andreabenini/beholder/hardware/rollie-Base.stl

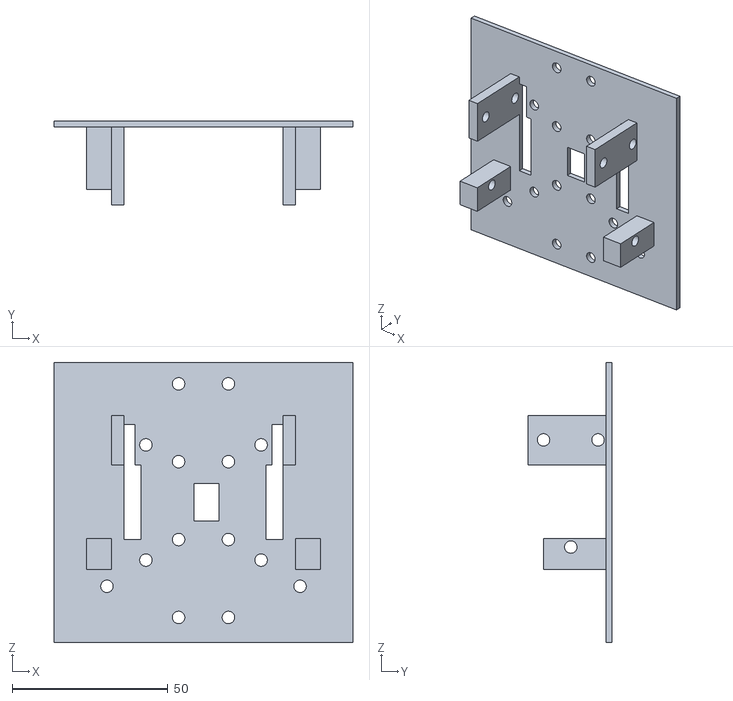
[picture p17: CAD file, 2023-04-09]
hardware/rollie-Base.stl
96.0 x 27.0 x 90.0
