andreabenini/beholder/hardware/rollie.3.0/rollie3-Right Bearing InnerConnector.stl

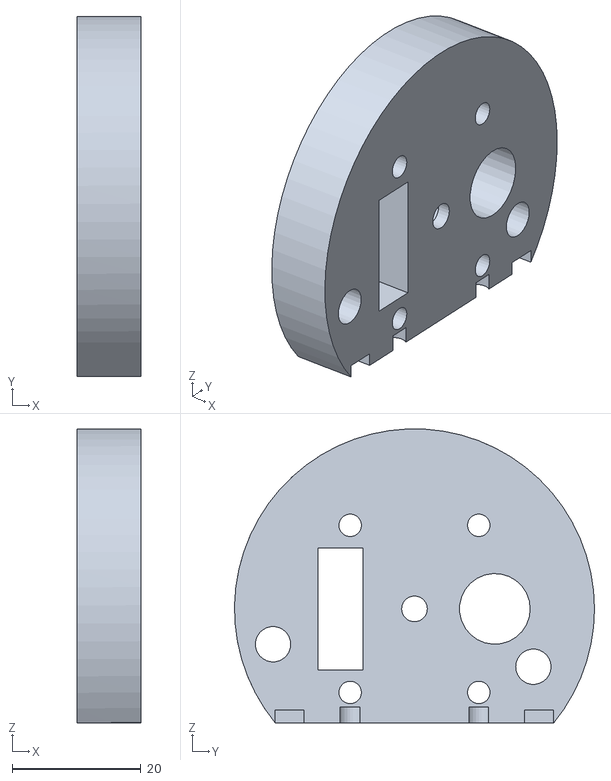
[picture p18: CAD file, 2023-11-20]
hardware/rollie.3.0/rollie3-Right Bearing InnerConnector.stl
10.0 x 56.0 x 45.7
