andreabenini/beholder/hardware/2.0/rollie2-wheel Right Inner Back.stl

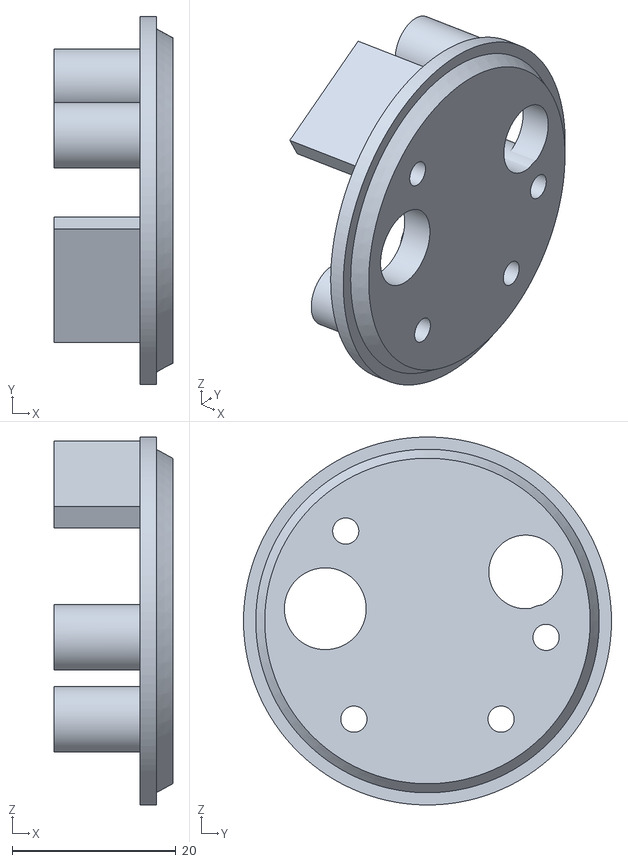
[picture p19: CAD file, 2023-09-27]
hardware/2.0/rollie2-wheel Right Inner Back.stl
14.5 x 45.0 x 45.0
