andreabenini/beholder/hardware/microguard.1.0/microguard-cylinder spacer1.stl

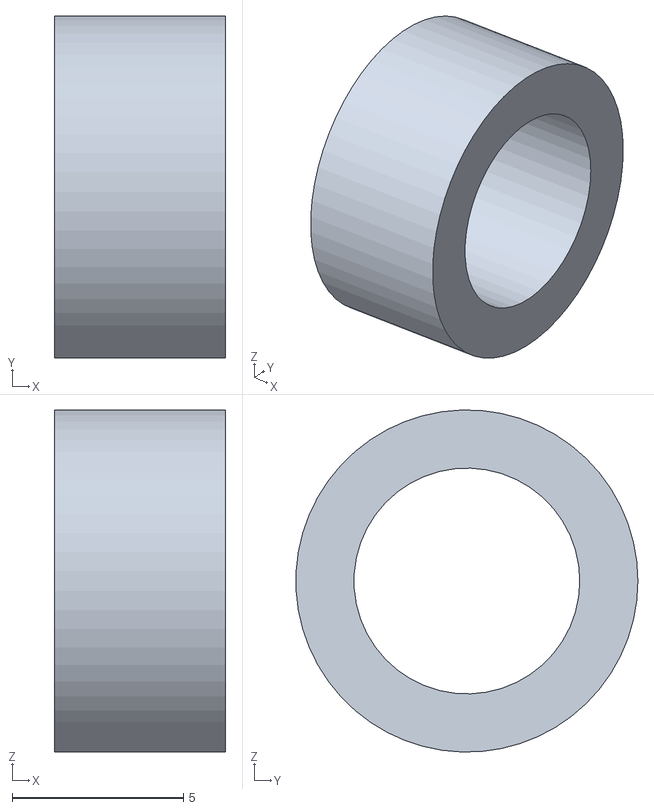
[picture p20: CAD file, 2024-03-03]
hardware/microguard.1.0/microguard-cylinder spacer1.stl
5.00 x 9.99 x 10.00
