andreabenini/beholder/hardware/rollie.3.0/rollie3-Right Bearing Inner Back.stl

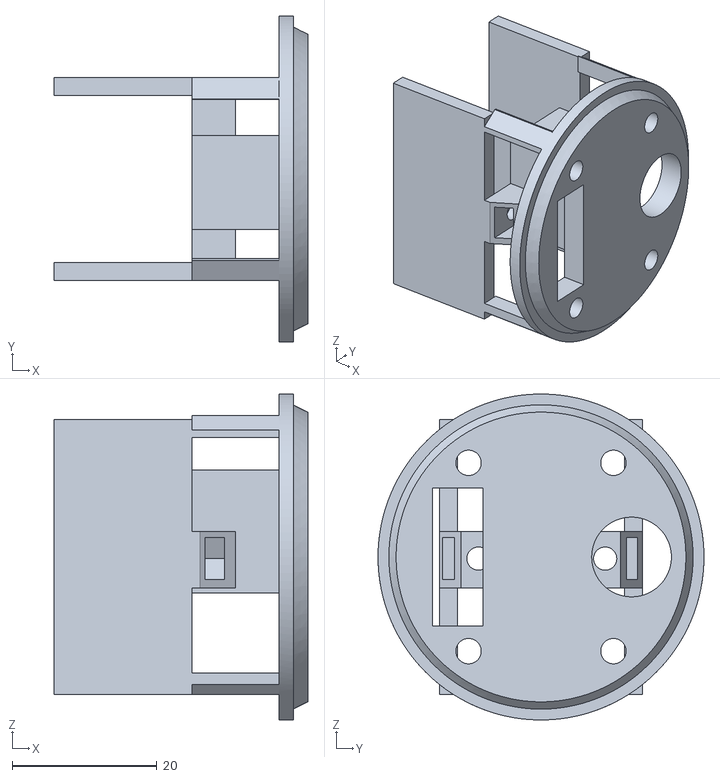
[picture p21: CAD file, 2023-11-20]
hardware/rollie.3.0/rollie3-Right Bearing Inner Back.stl
35.0 x 45.0 x 45.0
