andreabenini/beholder/hardware/2.0/rollie2-wheel Left Inner Back.stl

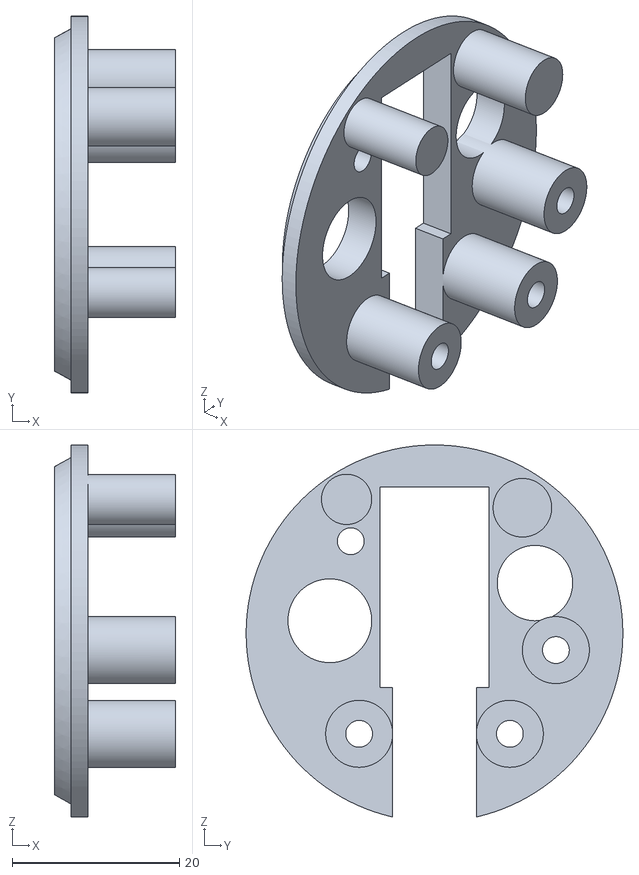
[picture p22: CAD file, 2023-09-27]
hardware/2.0/rollie2-wheel Left Inner Back.stl
14.5 x 45.0 x 44.4
