andreabenini/beholder/hardware/microguard.1.0/microguard-caster wheel holder.stl

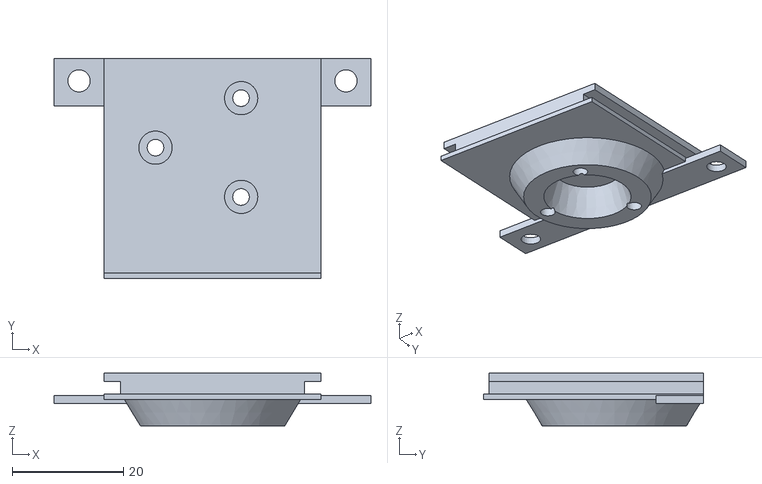
[picture p23: CAD file, 2024-03-01]
hardware/microguard.1.0/microguard-caster wheel holder.stl
57.0 x 39.5 x 9.50
