andreabenini/beholder/hardware/2.0/rollie2-Battery Holder Right.stl

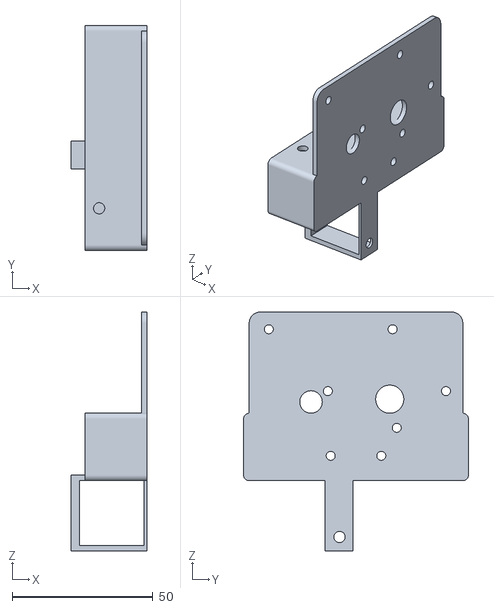
[picture p24: CAD file, 2023-09-22]
hardware/2.0/rollie2-Battery Holder Right.stl
27.0 x 80.0 x 85.0
