andreabenini/beholder/hardware/microguard.1.0/microguard-Controller Deck.stl

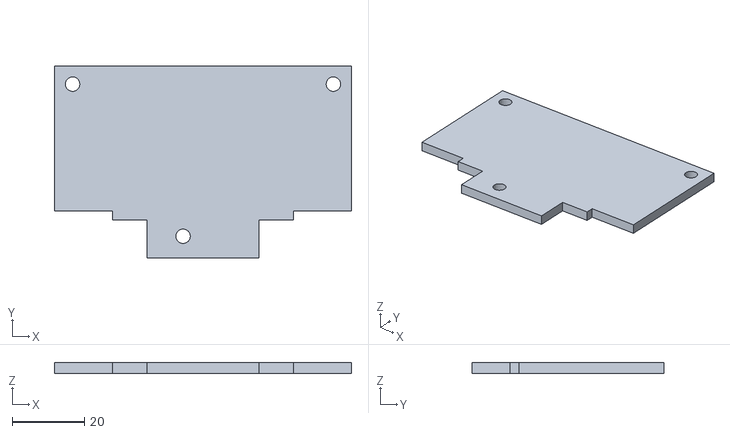
[picture p25: CAD file, 2024-03-01]
hardware/microguard.1.0/microguard-Controller Deck.stl
82.0 x 53.0 x 3.00
