andreabenini/beholder/hardware/rollie.3.0/rollie3-Left Pinion Gear.stl

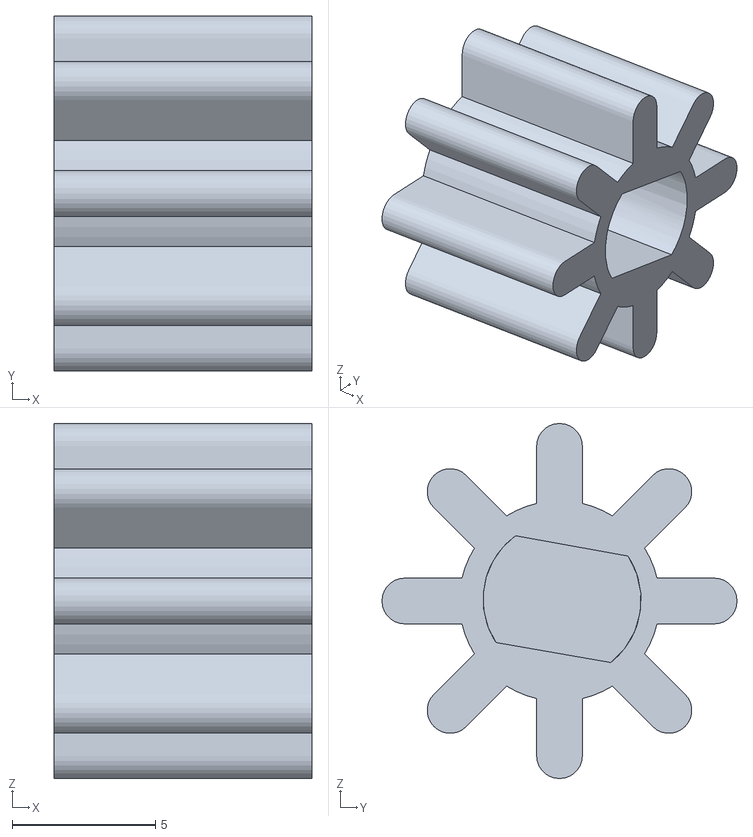
[picture p26: CAD file, 2023-11-13]
hardware/rollie.3.0/rollie3-Left Pinion Gear.stl
9.00 x 12.4 x 12.4
