andreabenini/beholder/hardware/2.0/rollie2-wheel Right Gear Pinion.stl

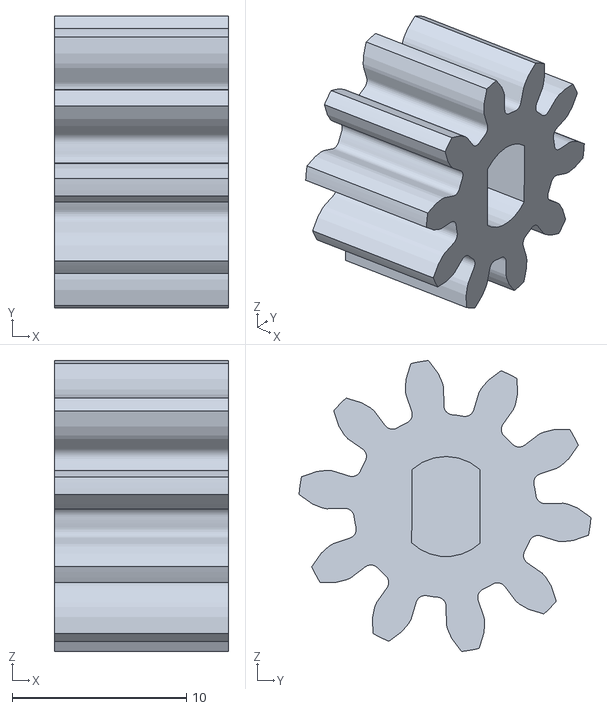
[picture p27: CAD file, 2023-07-04]
hardware/2.0/rollie2-wheel Right Gear Pinion.stl
10.0 x 16.7 x 16.7
