andreabenini/beholder/hardware/microguard.1.0/microguard-motor holder.stl

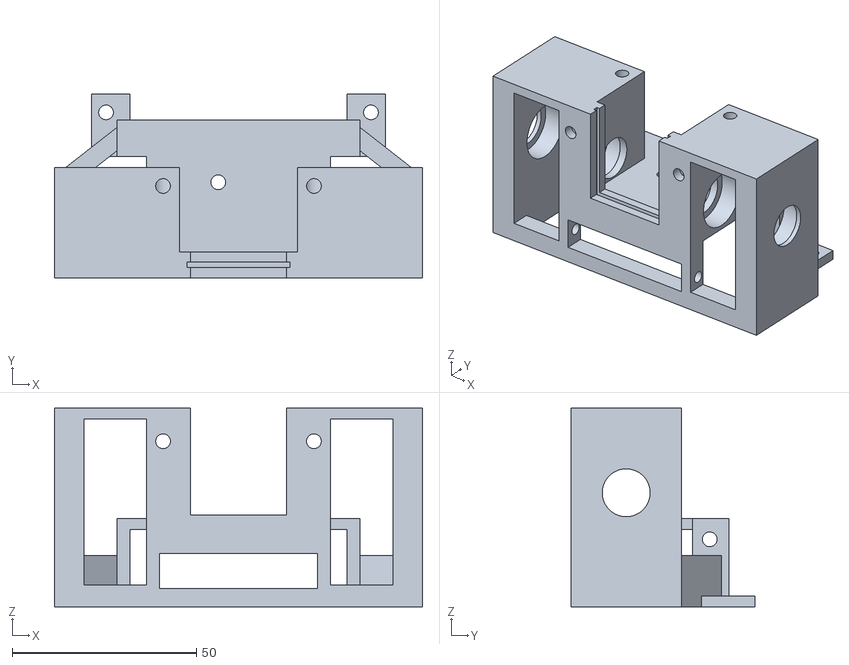
[picture p28: CAD file, 2024-02-28]
hardware/microguard.1.0/microguard-motor holder.stl
100.0 x 50.0 x 54.0
