andreabenini/beholder/hardware/rollie.3.0/rollie3-Left Bearing Inner Front.stl

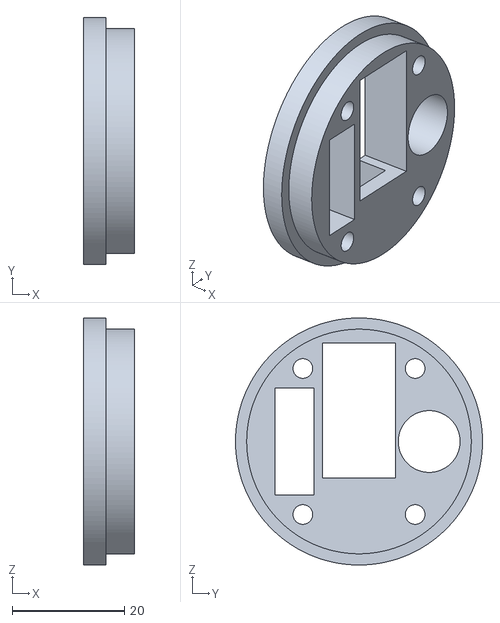
[picture p29: CAD file, 2023-11-12]
hardware/rollie.3.0/rollie3-Left Bearing Inner Front.stl
9.00 x 44.0 x 44.0
