andreabenini/beholder/hardware/2.0/rollie2-wheel Right Cap Front.stl

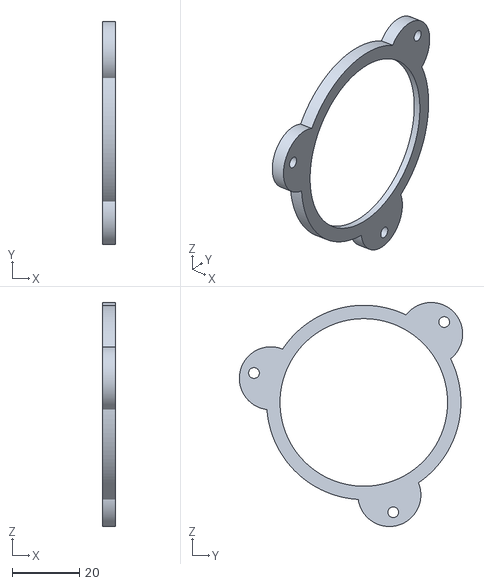
[picture p30: CAD file, 2023-06-18]
hardware/2.0/rollie2-wheel Right Cap Front.stl
4.00 x 66.7 x 66.9
