andreabenini/beholder/hardware/microguard.1.0/microguard-base plate.stl

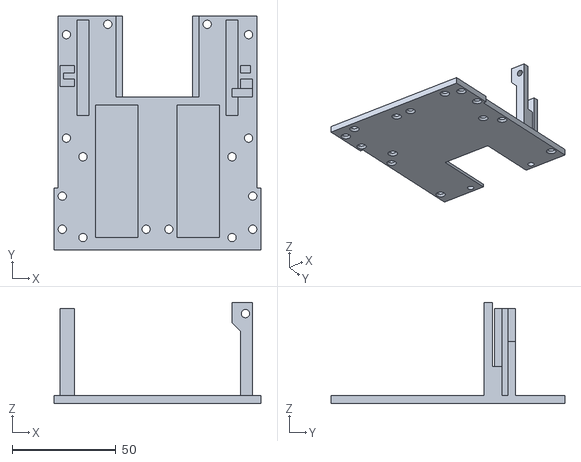
[picture p31: CAD file, 2024-02-24]
hardware/microguard.1.0/microguard-base plate.stl
100.0 x 113.0 x 49.0
