andreabenini/beholder/hardware/2.0/rollie2-Shoulder Right.stl

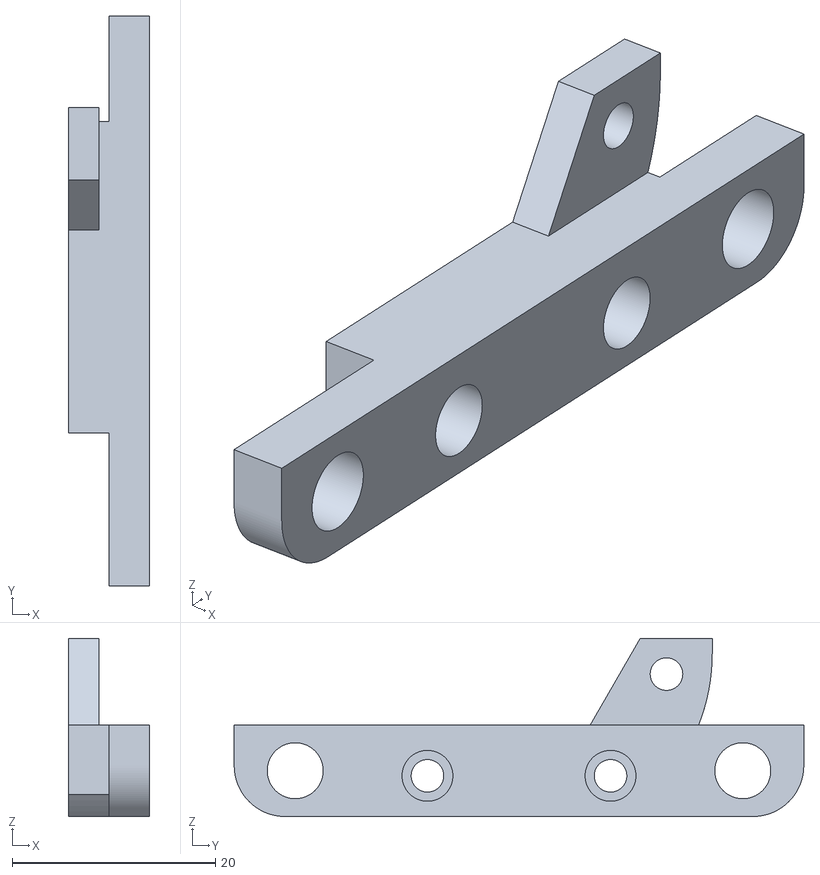
[picture p32: CAD file, 2023-06-18]
hardware/2.0/rollie2-Shoulder Right.stl
8.00 x 56.0 x 17.5
