andreabenini/beholder/hardware/microguard.1.0/microguard-mold side1.stl

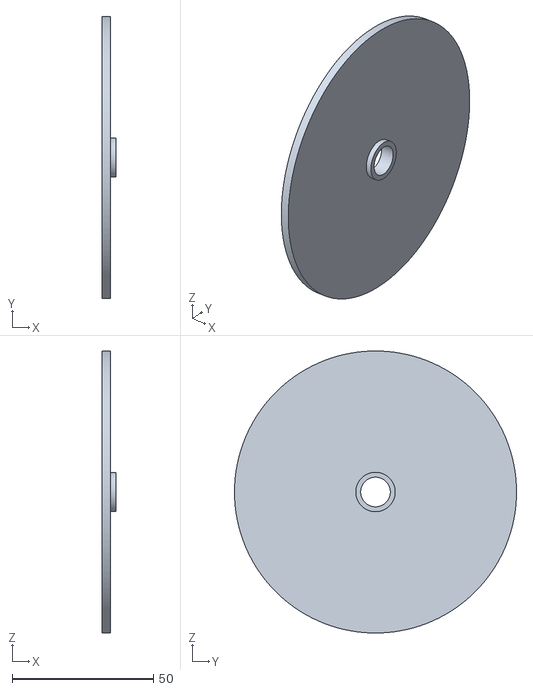
[picture p33: CAD file, 2024-01-27]
hardware/microguard.1.0/microguard-mold side1.stl
5.00 x 100.0 x 100.0
