andreabenini/beholder/hardware/rollie.3.0/rollie3-Left Bearing InnerConnector.stl

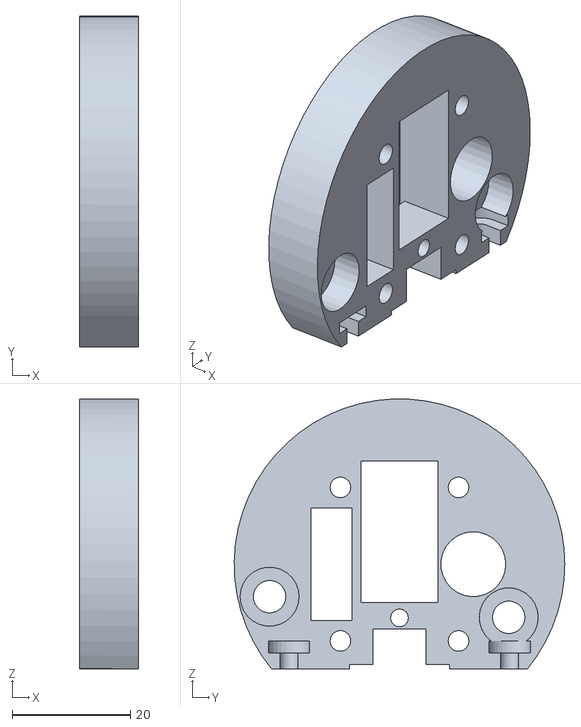
[picture p34: CAD file, 2023-11-11]
hardware/rollie.3.0/rollie3-Left Bearing InnerConnector.stl
10.0 x 56.0 x 45.7
