andreabenini/beholder/hardware/2.0/rollie2-servo Arm.stl

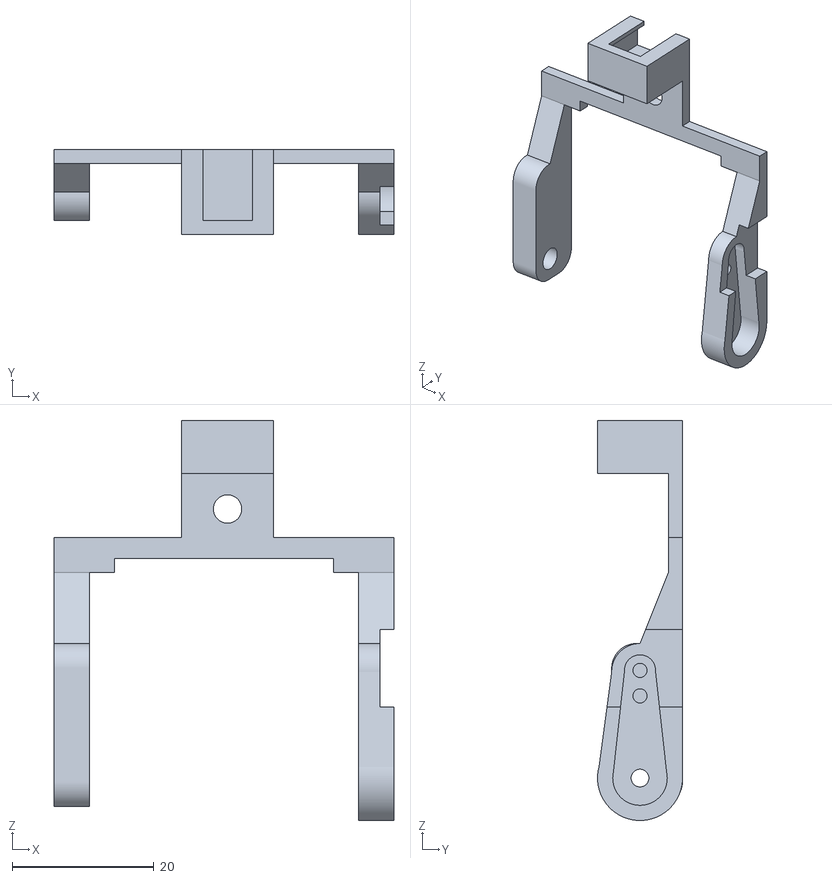
[picture p35: CAD file, 2023-06-15]
hardware/2.0/rollie2-servo Arm.stl
48.0 x 12.0 x 56.5
