andreabenini/beholder/hardware/microguard.1.0/microguard-mold side2.stl

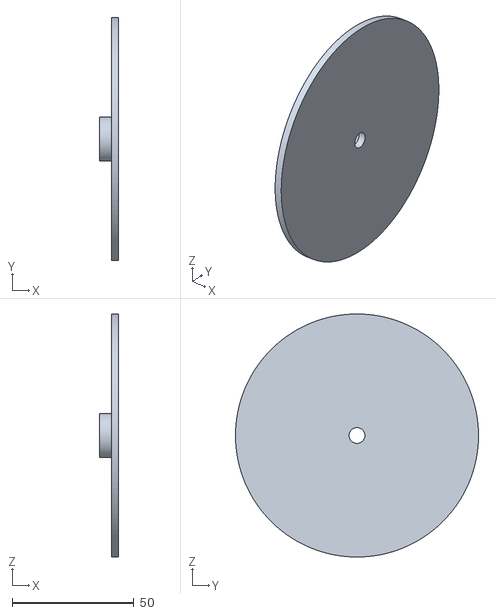
[picture p36: CAD file, 2024-01-27]
hardware/microguard.1.0/microguard-mold side2.stl
8.00 x 100.0 x 100.0
