andreabenini/beholder/hardware/rollie.3.0/rollie3-Holder Spacer.stl

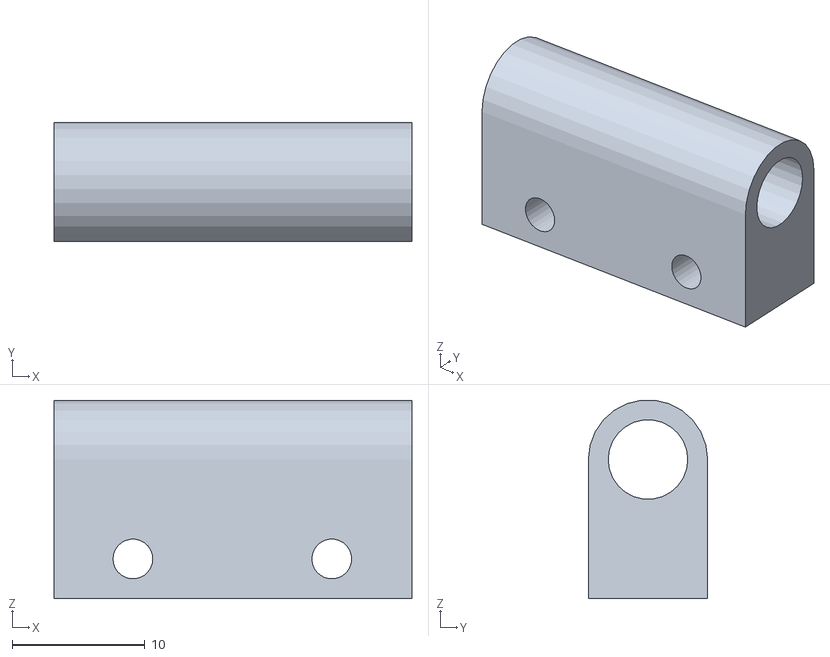
[picture p37: CAD file, 2023-11-10]
hardware/rollie.3.0/rollie3-Holder Spacer.stl
27.0 x 9.00 x 15.0
