andreabenini/beholder/hardware/microguard.1.0/microguard-gear left motor.stl

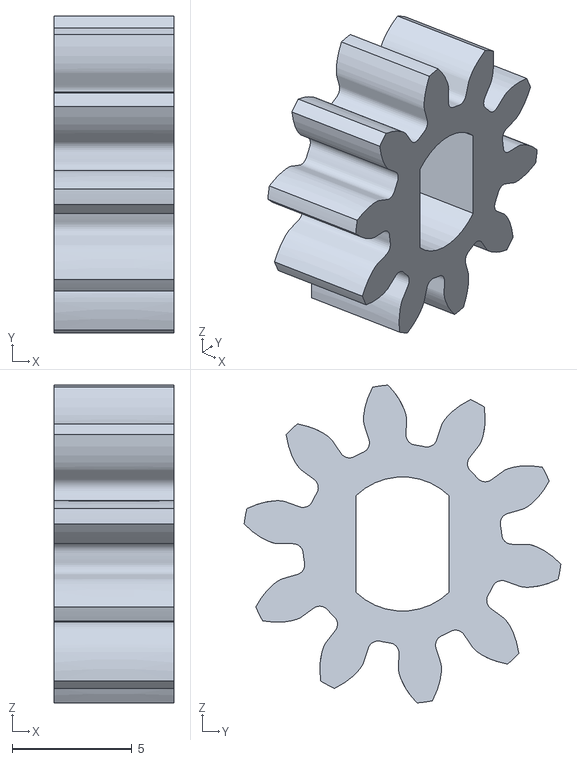
[picture p38: CAD file, 2024-01-25]
hardware/microguard.1.0/microguard-gear left motor.stl
5.00 x 13.2 x 13.3
