andreabenini/beholder/hardware/rollie.3.0/rollie3-servo Arm.stl

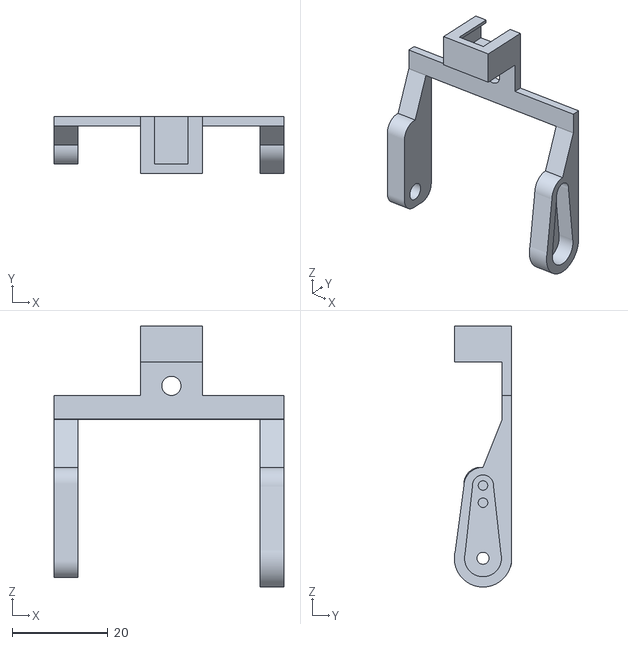
[picture p39: CAD file, 2023-11-10]
hardware/rollie.3.0/rollie3-servo Arm.stl
48.0 x 12.0 x 54.5
