andreabenini/beholder/hardware/2.0/rollie2-wheel Right Inner Front.stl

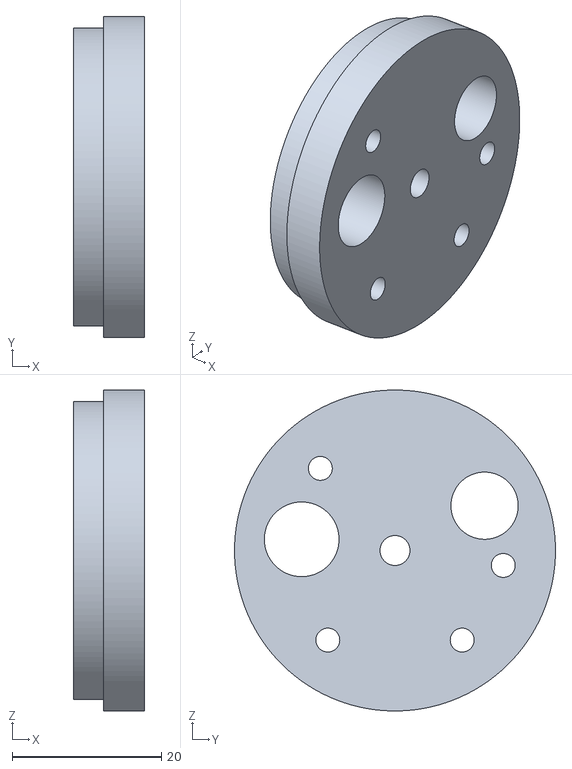
[picture p40: CAD file, 2023-06-06]
hardware/2.0/rollie2-wheel Right Inner Front.stl
9.50 x 43.0 x 43.0
