andreabenini/beholder/hardware/microguard.1.0/microguard-wheel.stl

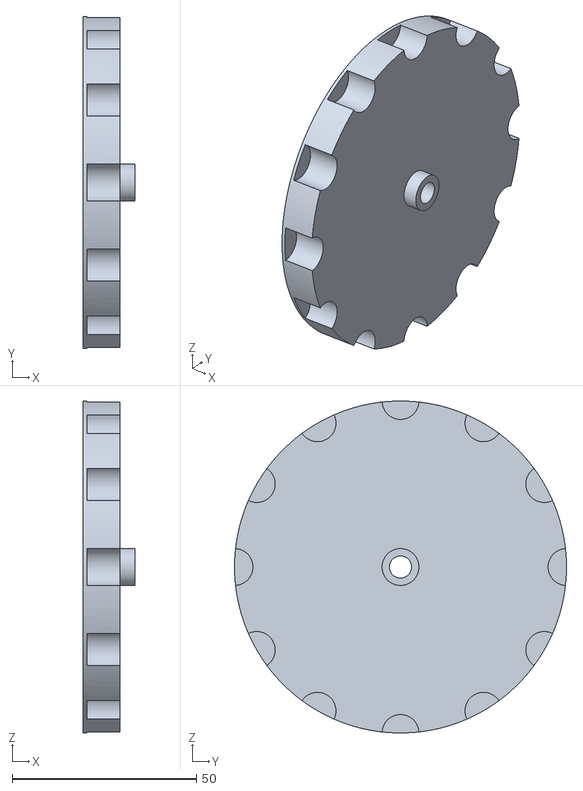
[picture p41: CAD file, 2024-01-10]
hardware/microguard.1.0/microguard-wheel.stl
14.0 x 90.0 x 90.0
