andreabenini/beholder/hardware/rollie.3.0/rollie3-ESP32 Holder.stl

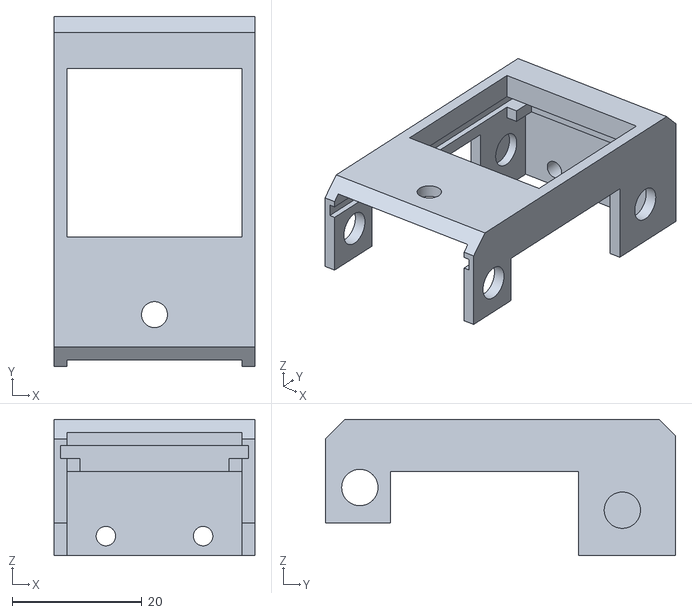
[picture p42: CAD file, 2023-11-10]
hardware/rollie.3.0/rollie3-ESP32 Holder.stl
31.0 x 54.0 x 21.0
