andreabenini/beholder/hardware/microguard.1.0/microguard-wheel outer.stl

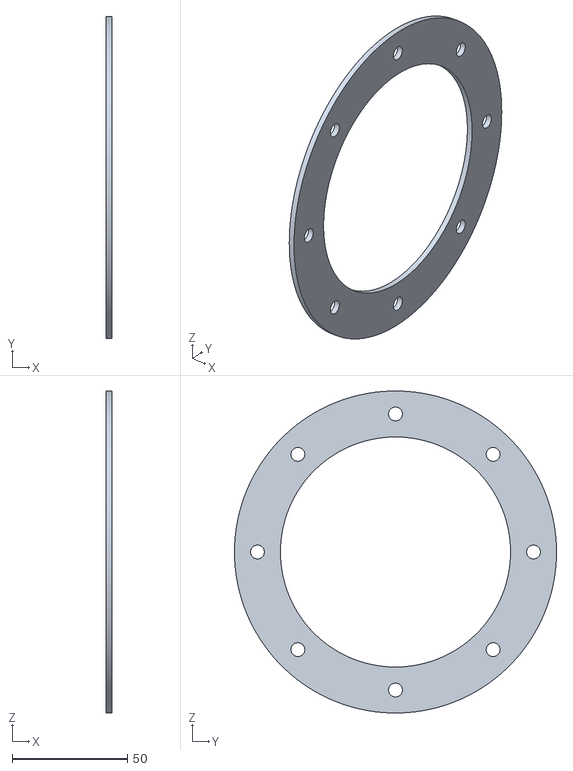
[picture p43: CAD file, 2024-01-10]
hardware/microguard.1.0/microguard-wheel outer.stl
2.50 x 140.0 x 140.0
