andreabenini/beholder/hardware/2.0/rollie2-wheel Right Wheel.stl

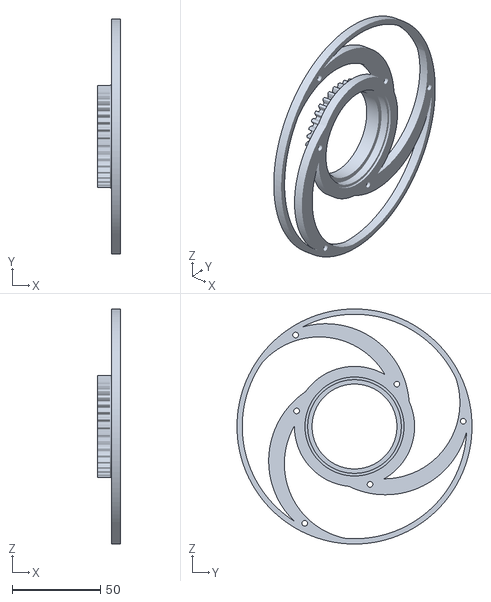
[picture p44: CAD file, 2023-06-02]
hardware/2.0/rollie2-wheel Right Wheel.stl
13.0 x 133.0 x 133.0
