andreabenini/beholder/hardware/microguard.1.0/microguard-wheel base.stl

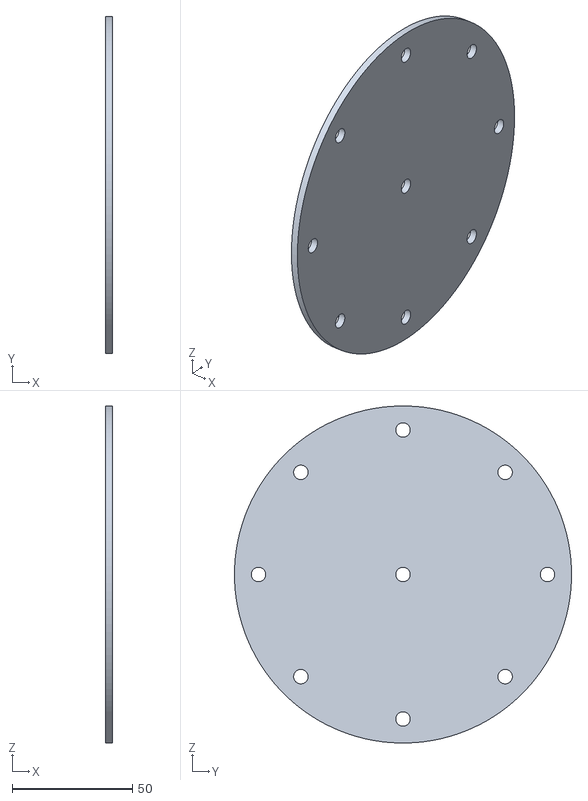
[picture p45: CAD file, 2024-01-10]
hardware/microguard.1.0/microguard-wheel base.stl
3.00 x 140.0 x 140.0
