andreabenini/beholder/hardware/2.0/rollie2-wheel Left Inner Front.stl

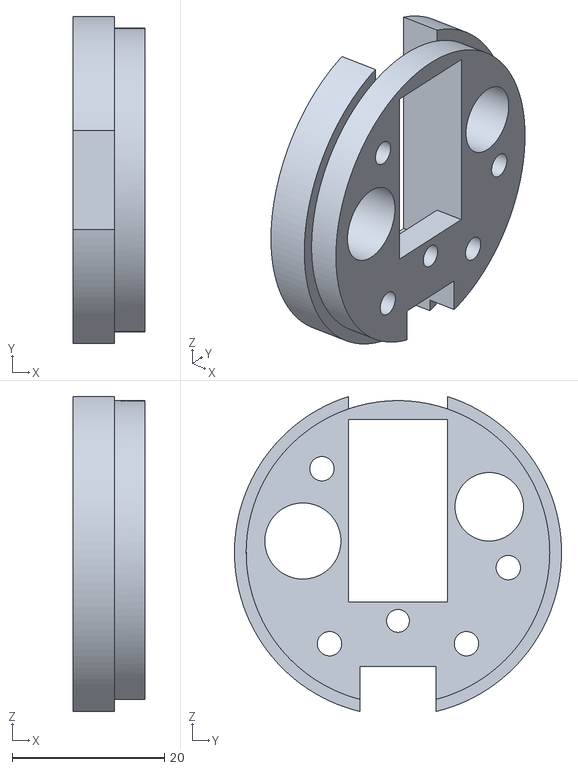
[picture p46: CAD file, 2023-05-14]
hardware/2.0/rollie2-wheel Left Inner Front.stl
9.50 x 43.0 x 41.4
