andreabenini/beholder/software/nanomicro/controller/src/icons.h

#ifndef _ICONS__H_
#define _ICONS__H_


typedef struct {
    byte xPos;
    byte yPos;
    byte width;
    byte height;
    const byte *data;
} iconType;


/**
 * https://javl.github.io/image2cpp/
 *      background              [black]
 *      invert image colors     [x]
 *      Code output format      [Adafruit GFXbitmapFont]
 *      Draw mode               [Vertical - 1 bit per pixel]
 */
const byte LOGO_eyeSleepy [] PROGMEM = {     // eye sleepy, 80x32px
    0x00, 0x00, 0x00, 0x10, 0x78, 0xf8, 0xe0, 0x80, 0x00, 0x00, 0x00, 0x00, 0x00, 0x00, 0x00, 0x00, 
    0x00, 0x00, 0x00, 0x00, 0x00, 0x00, 0x00, 0x00, 0x00, 0x00, 0x00, 0x00, 0x00, 0x00, 0x00, 0x00, 
    0x00, 0x00, 0x00, 0x00, 0x00, 0x00, 0x00, 0x00, 0x00, 0x00, 0x00, 0x00, 0x00, 0x00, 0x00, 0x00, 
    0x00, 0x00, 0x00, 0x00, 0x00, 0x00, 0x00, 0x00, 0x00, 0x00, 0x00, 0x00, 0x00, 0x00, 0x00, 0x00, 
    0x00, 0x00, 0x00, 0x00, 0x00, 0x00, 0x00, 0x00, 0x80, 0xe0, 0xf8, 0x78, 0x10, 0x00, 0x00, 0x00, 
    0x00, 0x00, 0x00, 0x80, 0xc0, 0xe1, 0xfb, 0x3f, 0x1f, 0x1e, 0x3c, 0x38, 0x70, 0xe0, 0xe0, 0xc0, 
    0xc0, 0x80, 0x80, 0x00, 0x00, 0x00, 0x00, 0x00, 0x00, 0x00, 0x00, 0x00, 0x00, 0x00, 0x00, 0x00, 
    0x00, 0x00, 0x00, 0x00, 0x00, 0x00, 0x00, 0x00, 0x00, 0x00, 0x00, 0x00, 0x00, 0x00, 0x00, 0x00, 
    0x00, 0x00, 0x00, 0x00, 0x00, 0x00, 0x00, 0x00, 0x00, 0x00, 0x00, 0x00, 0x80, 0x80, 0x80, 0xc0, 
    0xe0, 0xe0, 0x70, 0x70, 0x38, 0x1c, 0x1e, 0x1f, 0x3f, 0x7b, 0xf0, 0xc0, 0x80, 0x00, 0x00, 0x00, 
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
    0x07, 0x07, 0x03, 0x03, 0x01, 0x01, 0x00, 0x00, 0x00, 0x00, 0x00, 0x00, 0x00, 0x00, 0x00, 0x00, 
    0x00, 0x00, 0x00, 0x00, 0x00, 0xc0, 0xc0, 0xc0, 0xc0, 0xc0, 0xc0, 0xc0, 0xc0, 0xc0, 0x7f, 0x3f
};

#define LOGO_EYE_SLEEPY  0
#define LOGO_EYE_NORMAL  1
#define LOGO_EYE_ANGRY   2
#define LOGO_EYE_TARGET  3
const iconType Logo[] PROGMEM = {
    { .xPos=24, .yPos=4, .width=80, .height=32, .data=LOGO_eyeSleepy},
    { .xPos=24, .yPos=1, .width=64, .height=48, .data=LOGO_eyeNormal},
    { .xPos=22, .yPos=1, .width=88, .height=48, .data=LOGO_eyeAngry},
    { .xPos=22, .yPos=1, .width=88, .height=48, .data=LOGO_eyeTarget}
};

#endif
