andreabenini/beholder/software/esp32/master/main/camera.h

#ifndef CAMERA__H
#define CAMERA__H

#include "esp_camera.h"
#include "rom/gpio.h"               // GPIO definitions for camera blink
#include "freertos/FreeRTOS.h"      //
#include "freertos/task.h"          // xTaskCreate() define function
#include "esp_log.h"


#include "firmware.h"

#define TAG_CAMERA          "camera"


#define CONFIG_BOARD_ESP32CAM_AITHINKER 1
#define CONFIG_XCLK_FREQ 20000000 

// Freenove ESP32-WROVER CAM Board PIN Map
#if CONFIG_BOARD_WROVER_KIT
#define CAM_PIN_PWDN -1  //power down is not used
#define CAM_PIN_RESET -1 //software reset will be performed
#define CAM_PIN_XCLK 21
#define CAM_PIN_SIOD 26
#define CAM_PIN_SIOC 27

#define CAM_PIN_D7 35
#define CAM_PIN_D6 34
#define CAM_PIN_D5 39
#define CAM_PIN_D4 36
#define CAM_PIN_D3 19
#define CAM_PIN_D2 18
#define CAM_PIN_D1 5
#define CAM_PIN_D0 4
#define CAM_PIN_VSYNC 25
#define CAM_PIN_HREF 23
#define CAM_PIN_PCLK 22

#define FLASH_LED_GPIO GPIO_NUM_4               // GPIO pin connected to flash led

#endif

// ESP-EYE PIN Map
#if CONFIG_BOARD_CAMERA_MODEL_ESP_EYE
#define PWDN_GPIO_NUM    -1
#define RESET_GPIO_NUM   -1
#define XCLK_GPIO_NUM    4
#define SIOD_GPIO_NUM    18
#define SIOC_GPIO_NUM    23

#define Y9_GPIO_NUM      36
#define Y8_GPIO_NUM      37
#define Y7_GPIO_NUM      38
#define Y6_GPIO_NUM      39
#define Y5_GPIO_NUM      35
#define Y4_GPIO_NUM      14
#define Y3_GPIO_NUM      13
#define Y2_GPIO_NUM      34
#define VSYNC_GPIO_NUM   5
#define HREF_GPIO_NUM    27
#define PCLK_GPIO_NUM    25

#define FLASH_LED_GPIO GPIO_NUM_4               // GPIO pin connected to flash led

#endif


// AiThinker ESP32Cam PIN Map
#if CONFIG_BOARD_ESP32CAM_AITHINKER
#define CAM_PIN_PWDN 32
#define CAM_PIN_RESET -1 //software reset will be performed
#define CAM_PIN_XCLK 0
#define CAM_PIN_SIOD 26
#define CAM_PIN_SIOC 27

#define CAM_PIN_D7 35
#define CAM_PIN_D6 34
#define CAM_PIN_D5 39
#define CAM_PIN_D4 36
#define CAM_PIN_D3 21
#define CAM_PIN_D2 19
#define CAM_PIN_D1 18
#define CAM_PIN_D0 5
#define CAM_PIN_VSYNC 25
#define CAM_PIN_HREF 23
#define CAM_PIN_PCLK 22

#define FLASH_LED_GPIO GPIO_NUM_4               // GPIO pin connected to flash led

#endif



// TTGO T-Journal ESP32 Camera PIN Map
#if CONFIG_BOARD_CAMERA_MODEL_TTGO_T_JOURNAL
#define PWDN_GPIO_NUM      0
#define RESET_GPIO_NUM    15
#define XCLK_GPIO_NUM     27
#define SIOD_GPIO_NUM     25
#define SIOC_GPIO_NUM     23

#define Y9_GPIO_NUM       19
#define Y8_GPIO_NUM       36
#define Y7_GPIO_NUM       18
#define Y6_GPIO_NUM       39
#define Y5_GPIO_NUM        5
#define Y4_GPIO_NUM       34
#define Y3_GPIO_NUM       35
#define Y2_GPIO_NUM       17
#define VSYNC_GPIO_NUM    22
#define HREF_GPIO_NUM     26
#define PCLK_GPIO_NUM     21

#define FLASH_LED_GPIO GPIO_NUM_4               // GPIO pin connected to flash led

#endif


void      cameraStart(void);
esp_err_t cameraInit(uint8_t quality, uint8_t resolution);

void      cameraFlashErrorBlink(void);


#endif
