andreabenini/beholder/software/nanomicro/controller/src/display.h

#ifndef _DISPLAY__H_
#define _DISPLAY__H_
// #include <U8g2lib.h>
#include "SSD1306Ascii.h"
#include "SSD1306AsciiAvrI2c.h"


#include "icons.h"

void displayInit();
void displayEyes(byte image);


#endif
